serisman/pdk-temp-pwm-fan/pcb-u06/output/OSHPARK - Bottom.png

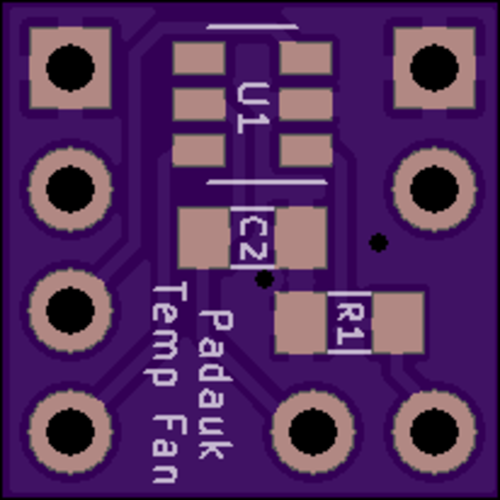
pcb-u06/output/OSHPARK - Bottom.png
