serisman/pdk-temp-pwm-fan/pcb-u06/output/OSHPARK - Top.png

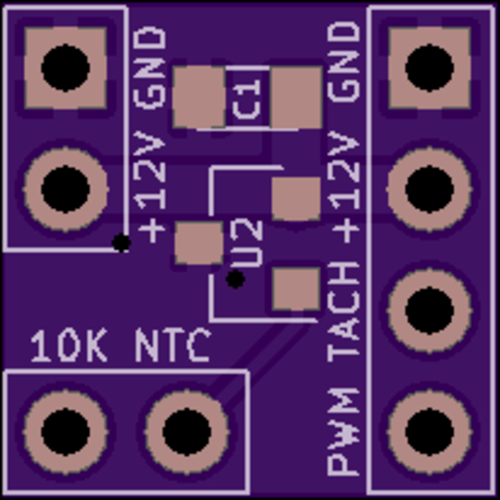
pcb-u06/output/OSHPARK - Top.png
