serisman/pdk-temp-pwm-fan/firmware/ntc.h

#ifndef __NTC_H__
#define __NTC_H__

// 10k NTC thermistor with 1k resistor to GND
#define NTC_1K_TRIGGER_2C     0x00
#define NTC_1K_TRIGGER_16C    0x01
#define NTC_1K_TRIGGER_26C    0x02
#define NTC_1K_TRIGGER_33C    0x03
#define NTC_1K_TRIGGER_40C    0x04
#define NTC_1K_TRIGGER_45C    0x05
#define NTC_1K_TRIGGER_50C    0x06
#define NTC_1K_TRIGGER_55C    0x07
#define NTC_1K_TRIGGER_59C    0x08
#define NTC_1K_TRIGGER_64C    0x09
#define NTC_1K_TRIGGER_68C    0x0A
#define NTC_1K_TRIGGER_72C    0x0B
#define NTC_1K_TRIGGER_76C    0x0C
#define NTC_1K_TRIGGER_80C    0x0D
#define NTC_1K_TRIGGER_84C    0x0E
#define NTC_1K_TRIGGER_88C    0x0F

// 10k NTC thermistor with 2k resistor to GND
#define NTC_2K_TRIGGER_NEG11C 0x00
#define NTC_2K_TRIGGER_2C     0x01
#define NTC_2K_TRIGGER_11C    0x02
#define NTC_2K_TRIGGER_18C    0x03
#define NTC_2K_TRIGGER_23C    0x04
#define NTC_2K_TRIGGER_28C    0x05
#define NTC_2K_TRIGGER_33C    0x06
#define NTC_2K_TRIGGER_37C    0x07
#define NTC_2K_TRIGGER_41C    0x08
#define NTC_2K_TRIGGER_45C    0x09
#define NTC_2K_TRIGGER_48C    0x0A
#define NTC_2K_TRIGGER_52C    0x0B
#define NTC_2K_TRIGGER_56C    0x0C
#define NTC_2K_TRIGGER_59C    0x0D
#define NTC_2K_TRIGGER_63C    0x0E
#define NTC_2K_TRIGGER_66C    0x0F

#endif //__NTC_H__
